gerb-ster/Echo-Reverb/images/IMG_3550.jpeg

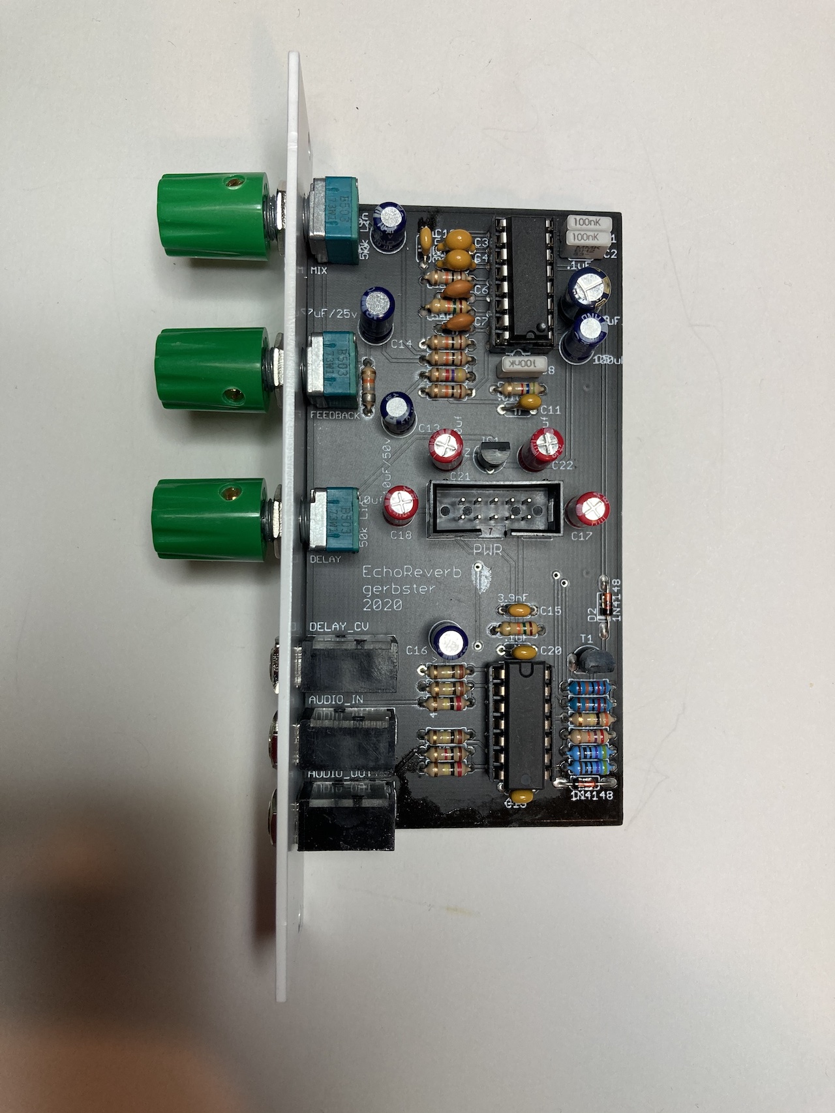
images/IMG_3550.jpeg
