gerb-ster/Echo-Reverb/images/IMG_3551.jpeg

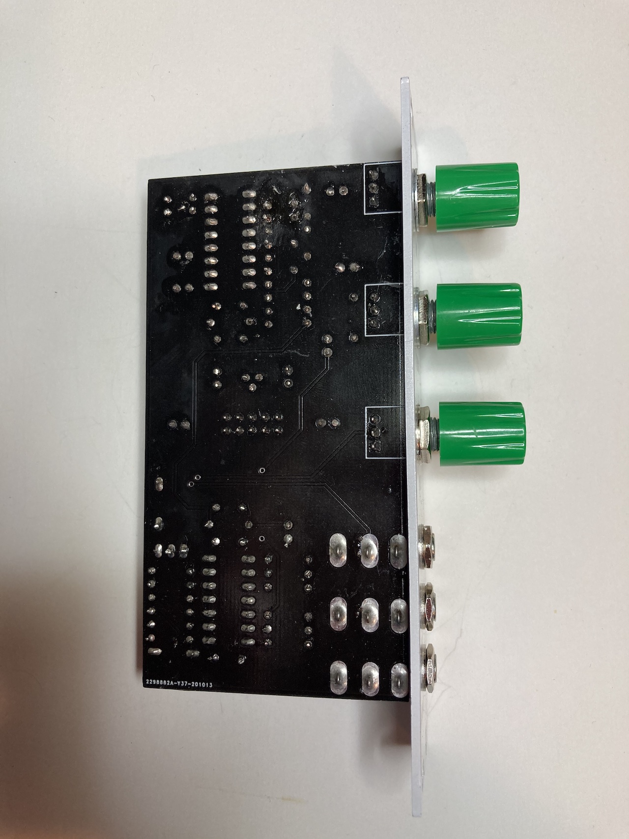
images/IMG_3551.jpeg
