gerb-ster/Echo-Reverb/images/IMG_3552.jpeg

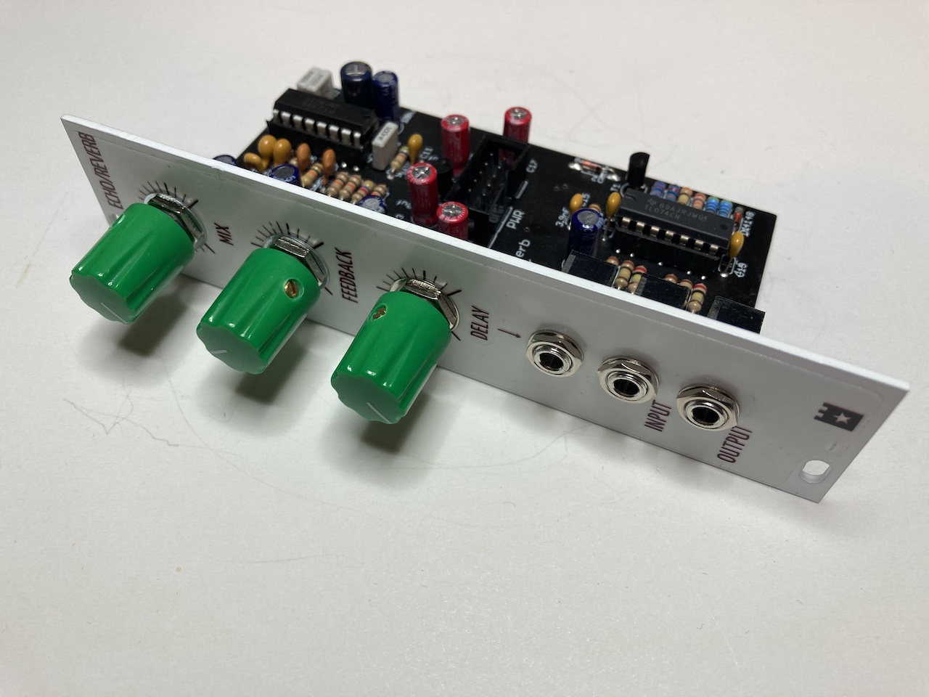
images/IMG_3552.jpeg
