gerb-ster/Echo-Reverb/images/IMG_3553.jpeg

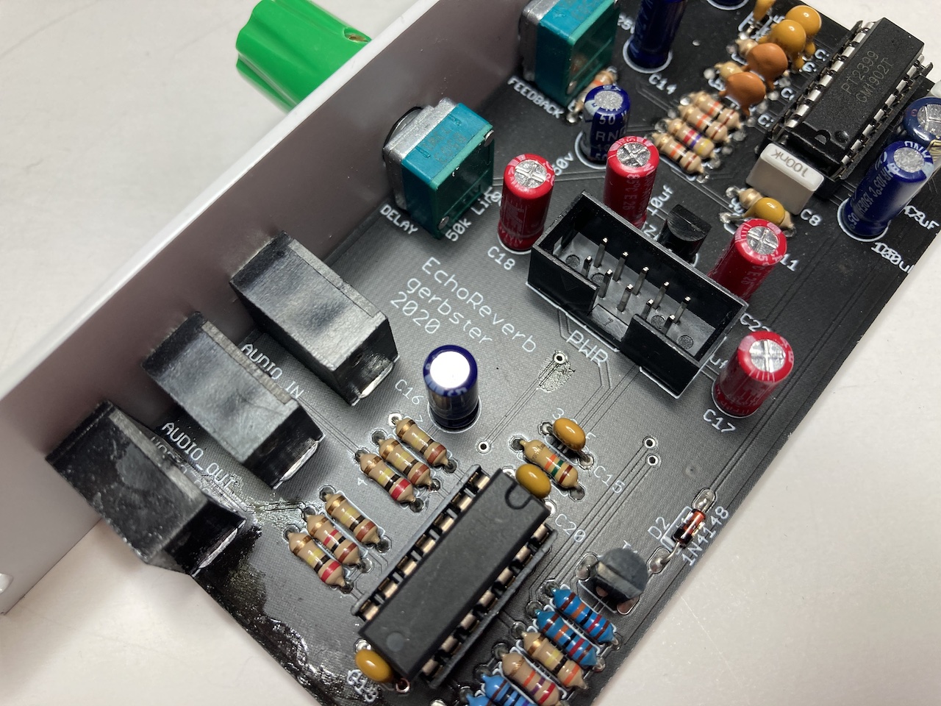
images/IMG_3553.jpeg
